paul0x1C/wasserschaden/kicad/rescue-backup/wasserschaden-2018-10-17-20-35-24.sch

## KiCad design kicad/rescue-backup/wasserschaden-2018-10-17-20-35-24.sch (2018-10-17)

Schematic: wasserschaden-2018-10-17-20-35-24.sch

Parts:
D1: D_5KPW_P12.70mm_Horizontal
D2, D3, D4: LED; LED_D3.0mm
IRFZ44N1: irlz44n
J1: valve out; TerminalBlock_Altech_AK300-2_P5.00mm
J2: 12V in; TerminalBlock_Altech_AK300-2_P5.00mm
R1: 20K; R_Axial_DIN0207_L6.3mm_D2.5mm_P7.62mm_Horizontal
R2, R3, R4: R; R_Axial_DIN0207_L6.3mm_D2.5mm_P7.62mm_Horizontal
U1: stepdown
U2: WeMos_mini; wemos-d1-mini-with-pin-header

Notes on the sheet:
+ -
